psylink-me/psylink/experimental/4_model3/calibrator/ai.py

# Inspired by https://colab.research.google.com/github/tensorflow/tensorflow/blob/8855f56500ff8efa449662a95fe69f24bb78c0a6/tensorflow/lite/micro/examples/hello_world/train/train_h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
import tensorflow as tf
from tensorflow import keras
from tensorflow.keras.models import load_model
import numpy as np
#import pandas as pd
#import matplotlib.pyplot as plt
import math
from config import DEFAULT_EPOCHS

LABEL_SEPARATOR = ','

class MyoAI:
    BATCH_SIZE = 64
    def __init__(self, window_size):
        # Set seed for experiment reproducibility
        seed = 1
        np.random.seed(seed)
        tf.random.set_seed(seed)
        self.num_channels = None
        self.model = None
        self.window_size = window_size
        self.training_data_generated = False

    def generate_training_data(self, values, train_split=0.8):
        # "values" is a flat array of [label, v1c1, v2c1, v3c1, ..., v1c2, ...]
        # where "v1c2" means "signal value at time step 1 of channel/electrode 2"

        self.num_channels = int((len(values[0]) - 1) / self.window_size)
        print('Found %d channels' % self.num_channels)

        print('Generating training data...')

        #window_size = int((len(values[0]) - 1.0) / self.num_channels)

        self.possible_labels = list(sorted(set(item[0] for item in values)))

        self.labels = np.full([len(values), len(self.possible_labels)], False, dtype=bool)
        #self.samples = np.zeros([len(values), len(values[0])-1])
        self.samples = np.zeros([len(values), self.num_channels, self.window_size])
        # Index meanings: self.samples[which_sample][which_signal][which_time_step] = signal_value

        # Split up the flat "values" list into distinct channels
        for sample_id, sample in enumerate(values):
            self.labels[sample_id][self.possible_labels.index(sample[0])] = True
            for channel in range(self.num_channels):
                start = 1 + channel * self.window_size
                end = 1 + (channel + 1) * self.window_size
                self.samples[sample_id][channel] = sample[start:end]

        #import pprint; pprint.pprint(self.samples)
        #import pprint; pprint.pprint(self.labels)

        train_split_index = int(len(self.samples) * train_split)

        self.labels, self.samples = unison_shuffled_copies(self.labels, self.samples)

        self.labels_train, self.labels_validate = np.split(self.labels, [train_split_index])
        self.samples_train, self.samples_validate = np.split(self.samples, [train_split_index])

        print('Generating training data... DONE')
        self.training_data_generated = True

    def generate_nn(self):
        if not self.training_data_generated:
            print("No training data generated yet!")
            return

        self.model = model = tf.keras.Sequential()

        #input_shape = (self.BATCH_SIZE, self.num_channels, self.window_size)
        input_shape = (self.num_channels, self.window_size)

        model.add(tf.keras.layers.SeparableConv1D(
            filters=128,
            kernel_size=5,
            input_shape=input_shape,
            #activation='selu',
        ))

        model.add(tf.keras.layers.SeparableConv1D(
            filters=128,
            kernel_size=3,
            #activation='relu',
        ))

        #conv_layer_1 = tf.keras.layers.Conv1D(
        #        filters=128,  # number of outputs
        #        kernel_size=5,
        #        strides=1,
        #        padding='same',
        #        groups=1,
        #        #activation='selu',
        #        input_shape=input_shape,
        #)
        #model.add(conv_layer_1)

        #conv_layer_2 = tf.keras.layers.Conv1D(
        #        filters=128,
        #        kernel_size=5,
        #        strides=1,
        #        padding='same',
        #        activation='selu',
        #)
        #model.add(conv_layer_2)

        model.add(tf.keras.layers.Flatten())

        #model.add(tf.keras.layers.Dense(128, activation='relu', input_shape=input_shape))

        for _ in range(3):
            model.add(tf.keras.layers.Dense(
                units=128,
                activation='relu',
                #bias_regularizer=tf.keras.regularizers.l1_l2(l1=1e-5, l2=1e-4),
                #activity_regularizer=tf.keras.regularizers.l1_l2(l1=1e-5, l2=1e-4),
                #kernel_regularizer=tf.keras.regularizers.l1_l2(l1=1e-5, l2=1e-4),
            ))

        model.add(tf.keras.layers.Dense(64, activation='relu'))

        output_layer = tf.keras.layers.Dense(len(self.possible_labels), activation='softmax')
        model.add(output_layer)

        model.compile(
                optimizer='adam', 
                loss='binary_crossentropy',
                metrics=['binary_accuracy']
        )
        #model.compile(optimizer='adam', loss='mse', metrics=['mae'])
        print(model)

        return model

    def nn_fit(self, epochs=DEFAULT_EPOCHS):
        print(f'samples_train shape: {self.samples_train.shape}')
        print(f'labels_train shape: {self.labels_train.shape}')
        history = self.model.fit(
                self.samples_train,
                self.labels_train,
                batch_size=self.BATCH_SIZE,
                epochs=epochs,
                validation_data=(self.samples_validate, self.labels_validate),
        )

    def predict(self, sample, num_channels):
        sample_array = np.array(sample).reshape((1, num_channels, self.window_size))
        #print(sample_array.shape)
        #raise SystemExit()
        prediction = self.model.predict(sample_array)
        label_id = np.argmax(prediction)
        return self.possible_labels[label_id]

    def save_model(self, filepath):
        self.model.save(filepath)
        filepath_labels = filepath + '.labels'
        with open(filepath_labels, 'w') as f:
            f.write(LABEL_SEPARATOR.join(self.possible_labels))

    def load_model(self, filepath):
        self.model = load_model(filepath)
        filepath_labels = filepath + '.labels'
        with open(filepath_labels, 'r') as f:
            self.possible_labels = f.read().strip().split(LABEL_SEPARATOR)


def unison_shuffled_copies(a, b):
    # https://stackoverflow.com/a/4602224
    assert len(a) == len(b)
    p = np.random.permutation(len(a))
    return a[p], b[p]
